NebraLtd/LoRa-mPCIe/hardware/Outputs/Assembly/LoRa_PCIe_GW-SPI_868M_GNSS_NON_TEMP/LoRa_PCIe_GW_full_asm.jpg

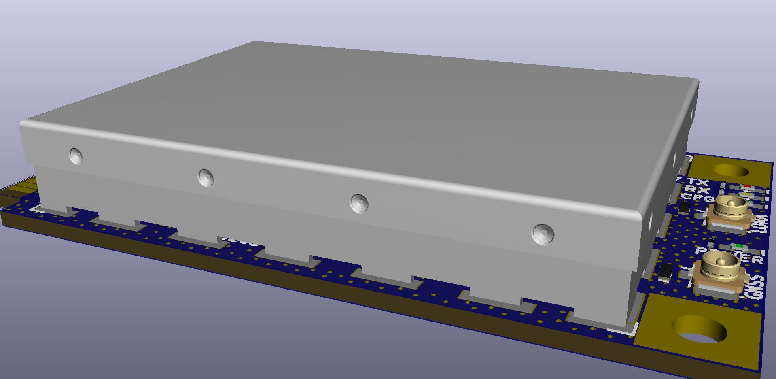
hardware/Outputs/Assembly/LoRa_PCIe_GW-SPI_868M_GNSS_NON_TEMP/LoRa_PCIe_GW_full_asm.jpg
