NebraLtd/LoRa-mPCIe/hardware/Outputs/Assembly/LoRa_PCIe_GW-SPI_US915M_GNSS_NON_TEMP/LoRa_PCIe_GW_shield_frame_asm_top.jpg

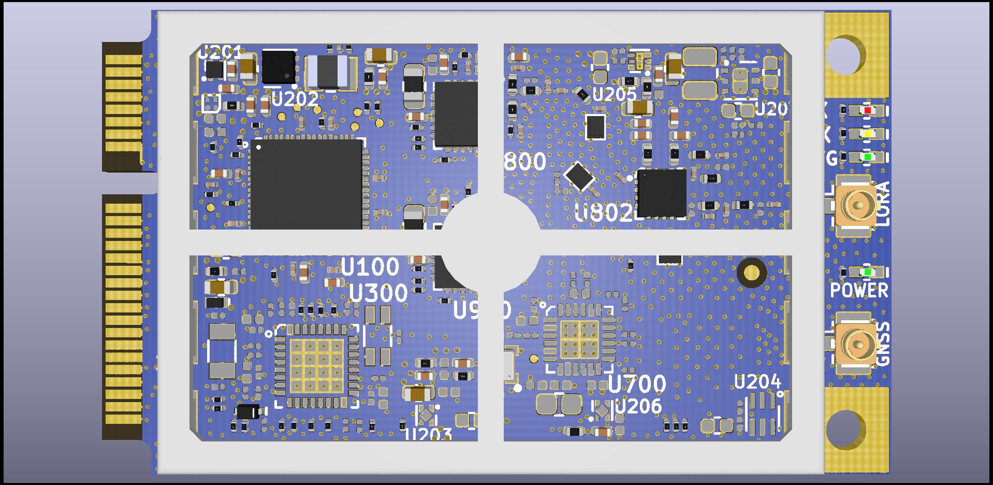
hardware/Outputs/Assembly/LoRa_PCIe_GW-SPI_US915M_GNSS_NON_TEMP/LoRa_PCIe_GW_shield_frame_asm_top.jpg
