NebraLtd/LoRa-mPCIe/hardware/Outputs/Assembly/LoRa_PCIe_GW-SPI_US915M_NON-GNSS_NON_TEMP/LoRa_PCIe_GW_asm_bottom.jpg

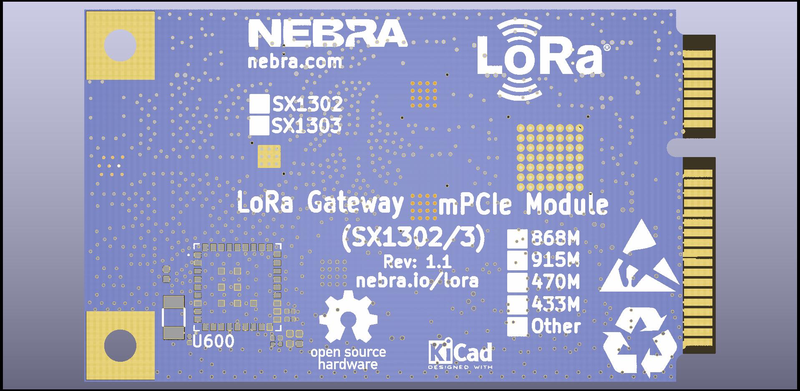
hardware/Outputs/Assembly/LoRa_PCIe_GW-SPI_US915M_NON-GNSS_NON_TEMP/LoRa_PCIe_GW_asm_bottom.jpg
